devboy/requencer/docs/production-check.md

# Pre-Production PCB Validation Checklist

Run this checklist before ordering PCBs or sourcing parts. Each section specifies what to read, what to check, and what constitutes PASS/WARN/FAIL.

## Output Format

For each section, produce a structured verdict:

```
## Section N: Title
**Verdict: PASS / WARN / FAIL**

| Check | Status | Detail |
|-------|--------|--------|
| ... | PASS/WARN/FAIL | ... |

**Issues found:**
- [Severity] Description — file:line — suggested fix
```

---

## Automated Checks (run first, do not duplicate)

Run these before starting the manual review. Record results for reference.

```bash
make hardware          # Full hardware pipeline (ato build → place → route → 3d → export)
make test-hw           # Unit tests (BOM parser, placement, collision)
cargo test             # Firmware tests (DAC driver, button mapping, MIDI)
```

If any automated check fails, fix before proceeding. Record the output of each for the report.

---

## Section 0: Component & Footprint Audit

**Verdict: PASS** (all CRITICAL, HIGH, and MEDIUM issues resolved)

**Run date:** 2026-03-18 | **Fixes applied:** 2026-03-18

Datasheet-level verification of every component's pin mapping, footprint, 3D model, and circuit usage. Custom footprints and fine-pitch QFN ICs are highest risk.

### CRITICAL — ~~Must fix before fabrication~~ FIXED 2026-03-18

| # | Component | Issue | Status |
|---|---|---|---|
| C1 | **DAC80508ZRTER** | Entire pin mapping wrong (15/16 pins). Remapped to match TI SLASEL1D §6. | **FIXED** |
| C2 | **BAT54S** | Pins 2/3 swapped (CATHODE↔COMMON). Corrected to ANODE=1, CATHODE=2, COMMON=3. | **FIXED** |
| C3 | **2N3904** | LCSC C18536 now KEC (1=E, 2=B, 3=C). Updated pin mapping + manufacturer. | **FIXED** |
| C4 | **PGA2350 I2C** | GP11/GP12 on different I2C instances. Reassigned to GP12(SDA)+GP13(SCL), both I2C0 F3. | **FIXED** |

### HIGH — ~~Should fix before fabrication~~ FIXED 2026-03-18

| # | Component | Issue | Status |
|---|---|---|---|
| H1 | **IS31FL3216A** | I2C address comments swapped for led_b/led_c. Comments corrected to match wiring. | **FIXED** |
| H2 | **PB6149L** | LED polarity confirmed from mechanical drawing: L1(+)=anode=pin5, L2(−)=cathode=pin6. Matches design. Drawing saved to `components/PB6149L/images/`. | **VERIFIED** |
| H3 | **PB6149L** | Switch pin spacing confirmed 5.08mm×5.08mm, pin Ø1.0mm matches footprint drill. Drawing saved to `components/PB6149L/images/`. | **VERIFIED** |

### MEDIUM — ~~Should fix, not blocking~~ FIXED 2026-03-18

| # | Component | Issue | Status |
|---|---|---|---|
| M1 | **PRTR5V0U2X** | SOT-143B pad 1 widened to 1.2mm for polarity ID per SOT-143B spec. | **FIXED** |
| M2 | **DAC80508ZRTER** | Added WQFN-16 3D model reference to footprint. | **FIXED** |
| M3 | **DAC80508ZRTER** | EP pad corrected from 1.7x1.7mm to 1.6x1.6mm per datasheet. | **FIXED** |
| M4 | **R1206** | Added R1206 to SUFFIX_MODEL_MAP in add_3d_models.py. | **FIXED** |
| M5 | **WQP518MA** | Rect pad moved from pin 2 to pin 1 (Tip) per KiCad convention. | **FIXED** |
| M6 | **PJ366ST** | Added missing closing paren to keepout zone polygon in PJ366ST-full.kicad_mod. | **FIXED** |

### LOW — Informational

| # | Component | Issue |
|---|---|---|
| L1 | IS31FL3216A | IN pin left floating. Tie to GND if audio mode unused to prevent noise. |
| L2 | OPA4171AIPWR | 3D model has 0.2625mm X offset — visually verify alignment. |
| L3 | PRTR5V0U2X | LCSC C2827688 manufacturer "TECH PUBLIC" vs design "Nexperia". Functional equivalent. |
| L4 | H11L1S | LCSC C78589 manufacturer "EVERLIGHT" vs .ato "Lite-On". Both valid H11L1S makers. |
| L5 | BAT54S | LCSC C7420333 manufacturer "hongjiacheng" vs .ato "Nexperia". Budget clone. |
| L6 | USB_C_Receptacle | Only 1 shield/mounting pad. Check TYPE-C-31-M-12 datasheet for required mechanical pads. |
| L7 | USB_C_Receptacle | 3D model uses USB4085 as stand-in. Visual alignment unverified. |
| L8 | FPC_18P_05MM | Defined but unused. Dead code (alternate display connector). |
| L9 | ResistorNetwork9 | Defined but unused. Dead code. |
| L10 | FOJAN parts | C2930086 (29.4kΩ) and C2907540 (82Ω 1206) have high LCSC numbers — check stock. |
| L11 | 1206 resistor | Only 1206 part in otherwise all-0402/0603 design. Confirm intentional (power handling). |
| L12 | PGA2350 | LCSC C0000 placeholder — Pimoroni not on LCSC. BOM generation will need manual entry. |
| L13 | Dead generator code | `generate_footprints.py` has unused `make_wqp518ma()` with different pin positions than actual footprint. |

### Components PASSED (no issues)

| Component | Package | Pin mapping | Footprint | Circuit usage |
|---|---|---|---|---|
| IS31FL3216A | QFN-28 (0.45mm) | PASS (all 28+EP) | PASS | PASS |
| OPA4171AIPWR | TSSOP-14 (0.65mm) | PASS (standard quad op-amp) | PASS | PASS |
| 2N7002 | SOT-23 | PASS | PASS | PASS |
| AMS1117-3.3 | SOT-223 | PASS | PASS | PASS |
| B5819W | SOD-123 | PASS | PASS | PASS |
| H11L1S | SOP-6 (2.54mm) | PASS | PASS (wide-body valid for optocoupler) | PASS |
| EurorackPowerHeader16 | 2x8 shrouded | PASS (Doepfer standard) | PASS | PASS |
| ShroudedHeader2x16 | 2x8x2 | PASS (32-pin mirror) | PASS | PASS |
| ShroudedSocket2x16 | 2x8x2 | PASS | PASS | PASS |
| FPC_32P_05MM | 32-pin FPC | PASS (ST7796 match) | PASS | PASS |
| ResArray4x0603 | 0603x4 convex | PASS | PASS | PASS |
| PGA2350 (footprint) | 64-pin PGA | PASS (positions) | PASS | — |
| WQP518MA | THT mono jack | PASS | PASS | PASS |
| PJ366ST | THT stereo jack | PASS | PASS | PASS |
| EC11E | THT encoder | PASS | PASS | PASS |
| PJS008U | MicroSD vertical | PASS (SPI mode) | PASS | PASS |
| Precision resistors | 0603 0.1% | PASS (pitch-critical paths only) | PASS | PASS |

---

## Section 1: RP2350 GPIO Function-Select Compliance

**Why:** The RP2350 has fixed hardware function-select — SPI and UART peripherals can only be assigned to specific GPIOs. This was the #1 class of errors in the 2026-03-10 report (C1-C4).

### Files to read
- `hardware/boards/elec/src/mcu.ato` — all `pga.GPxx ~ signal_name` lines
- `crates/firmware/src/main.rs` — pin assignments (search for `PIN_`)
- `crates/firmware/src/pins.rs` — type aliases for pins
- RP2350 datasheet GPIO function table (Section 1.4.3, Table 2)

### What to check

**SPI0 pins (display + SD card):**

| Function | Valid GPIOs (RP2350) | Check mcu.ato assigns to | Check firmware uses |
|---|---|---|---|
| SPI0_RX (MISO) | GP0, GP4, GP16, GP20 | one of these | same pin |
| SPI0_TX (MOSI) | GP3, GP7, GP19, GP23 | one of these | same pin |
| SPI0_SCK | GP2, GP6, GP18, GP22 | one of these | same pin |
| SPI0_CSn | GP1, GP5, GP17, GP21 | one of these | same pin |

**SPI1 pins (DAC):**

| Function | Valid GPIOs (RP2350) | Check mcu.ato assigns to | Check firmware uses |
|---|---|---|---|
| SPI1_RX (MISO) | GP8, GP12, GP24, GP28 | one of these (if used) | same pin |
| SPI1_TX (MOSI) | GP11, GP15, GP27, GP31 | one of these | same pin |
| SPI1_SCK | GP10, GP14, GP26, GP30 | one of these | same pin |
| SPI1_CSn | GP9, GP13, GP25, GP29 | one of these (if used) | same pin |

**UART1 pins (MIDI):**

| Function | Valid GPIOs (RP2350) | Check mcu.ato assigns to | Check firmware uses |
|---|---|---|---|
| UART1_TX | GP4, GP8, GP12, GP16, GP20, GP24 | one of these | same pin |
| UART1_RX | GP5, GP9, GP13, GP17, GP21, GP25 | one of these | same pin |

**ADC pins (CV inputs):**

| Function | Valid GPIOs (RP2350) | Check mcu.ato assigns to |
|---|---|---|
| ADC4-7 | GP40-GP43 only | cv_a through cv_d |

### Pass criteria
- **PASS:** Every peripheral pin in mcu.ato is on a valid GPIO for that function AND matches firmware
- **WARN:** pins.rs type aliases don't match main.rs (cosmetic but confusing)
- **FAIL:** Any peripheral pin assigned to a GPIO that doesn't support that function, or mcu.ato/firmware mismatch

---

## Section 2: Board-to-Board Connector Pin Matching

**Why:** A single swapped pin on the 2x16 connector means rework or dead board.

### Files to read
- `hardware/boards/elec/src/board-connector.ato` — both `BoardConnectorInterface` and `BoardConnectorSocket`
- `hardware/boards/parts/ShroudedHeader2x16/ShroudedHeader2x16.ato` — header pinout
- `hardware/boards/parts/ShroudedSocket2x16/ShroudedSocket2x16.ato` — socket pinout

### What to check

1. **Pin-for-pin signal matching:** For each pin position (1-32) on both header_a and header_b, verify that the signal name on the Interface (main board male) matches the signal name on the Socket (control board female). Build a comparison table:

   | Pin | Header A Interface (main) | Header A Socket (control) | Match? |
   |-----|--------------------------|--------------------------|--------|
   | 1   | ...                      | ...                      |        |

2. **Physical orientation:** When the main board is below the control board:
   - Male headers point UP from main board
   - Female sockets point DOWN from control board
   - Pin 1 orientation must be consistent (keyed by shroud)
   - Verify the shroud key slot faces the same direction on both boards

3. **Power pin placement:** Verify power pins (GND, 3.3V, 5V, +12V, -12V) are doubled for current capacity and placed at connector edges (not in the middle where signal integrity matters more).

4. **No signal-to-power shorts:** Verify no signal name on one side maps to a power pin on the other side.

### Pass criteria
- **PASS:** All pins match 1:1 between Interface and Socket, orientation is correct
- **FAIL:** Any signal mismatch between corresponding pins, or power pin in wrong position

---

## Section 3: Signal Path Integrity

**Why:** Catches wiring errors, wrong gain, missing protection, floating pins.

### Files to read
- `hardware/boards/elec/src/main.ato` — main board top-level
- `hardware/boards/elec/src/control.ato` — control board top-level
- `hardware/boards/elec/src/mcu.ato` — MCU connections
- `hardware/boards/elec/src/dac-output.ato` — DAC + op-amp + level shifter
- `hardware/boards/elec/src/io-jacks.ato` — jack connections
- `hardware/boards/elec/src/led-driver.ato` — LED driver chain
- `hardware/boards/elec/src/midi.ato` — MIDI I/O circuits
- `hardware/boards/elec/src/input-protection.ato` — CV/clock/reset input protection
- `hardware/boards/elec/src/power.ato` — power supply
- `hardware/boards/elec/src/display.ato` — display connection
- Relevant part .ato files in `hardware/boards/parts/`

### Trace each path end-to-end

For each functional block below, trace the complete signal path from source to destination. Verify correct component values, topology, and power rails at each stage.

#### 3a. Pitch CV (4 channels)
- DAC OUT4-7 → op-amp (gain=2, offset from precision reference) → 470Ω protection → jack tip
- Check: gain resistors (10k/10k for gain=2), offset resistors (15k/10k for -2V offset), 0.1% tolerance on precision path
- Check: op-amp powered from ±12V (not 5V — needs negative swing)
- Check: reference buffer present (no loading on precision divider)
- Expected range: -2V to +8V (10 octaves, 1V/oct)

#### 3b. Gate CV (4 channels)
- DAC OUT0-3 → op-amp (unity gain buffer) → 470Ω protection → jack tip
- Check: unity gain (feedback direct from output to inverting input)
- Expected range: 0-5V

#### 3c. Velocity CV (4 channels)
- DAC OUT → op-amp (gain ≈ 1.6) → protection → jack tip
- Expected range: 0-8V

#### 3d. Mod CV (4 channels)
- DAC OUT → op-amp (inverting gain=2, offset=+5V) → protection → jack tip
- Check: needs negative output, op-amp on ±12V
- Expected range: -5V to +5V

#### 3e. Button scan
- GPIO → 74HC165 chain: CLK (shared), LATCH (shared), DATA (series QH→SER)
- Check: first SR's SER tied to GND, last SR's QH goes to MCU
- Check: CLK_INH tied LOW on all
- Check: pull-ups on all button inputs (via SIP resistor networks)
- Check: unused inputs tied to VCC (no floating)

#### 3f. LED drive
- MCU GPIO → TLC5947 chain: SIN, SCLK, XLAT, BLANK (shared)
- Check: SIN daisy-chains through SOUT→SIN
- Check: BLANK active-high (HIGH = outputs off)
- Check: VCC from 3.3V, LED anodes from 5V
- Check: IREF resistor value → expected max current per channel

#### 3g. MIDI
- **OUT:** MCU UART TX → 220Ω → TRS jack (Tip=data, Ring=VCC per Type A)
- **IN:** TRS jack → 220Ω → optocoupler LED → MCU UART RX
- Check: optocoupler LED polarity (anode toward Ring/VCC source, cathode toward Tip/data)
- Check: protection diode across opto LED (anti-parallel, correct polarity)
- Check: opto output pull-up to 3.3V

#### 3h. Clock/Reset I/O
- **Input:** jack tip → board connector → voltage divider (22k/10k) → BAT54S clamp → 100nF filter → MCU GPIO
- **Output:** MCU GPIO → 1kΩ base resistor → NPN (2N3904) → 1kΩ collector to 5V → jack tip
- Check: divider ratio maps 10V input to < 3.3V
- Check: NPN inverts logic (firmware must account for this)

#### 3i. Display
- MCU SPI0 (MOSI, SCK, CS) + DC + BL + RST → FPC connector
- Check: RST has RC delay circuit (10kΩ × 100nF ≥ 10µs)
- Check: backlight via N-channel MOSFET with gate pull-down

#### 3j. SD card
- MCU SPI0 (MOSI, MISO, SCK) + CS + CD → SD connector
- Check: MISO actually connected (SPI0_RX pin)
- Check: card detect signal routed to MCU

#### 3k. USB-C
- MCU USB DP/DM → 27Ω series → USB-C connector
- Check: 5.1kΩ CC1/CC2 pull-downs present
- Check: ESD protection (PRTR5V0U2X or similar) on data lines
- Check: shield → GND

#### 3l. Encoders
- Encoder A/B/SW → pull-ups (10kΩ to 3.3V) + debounce caps (100nF) → board connector → MCU GPIO
- Check: RC time constant appropriate (10kΩ × 100nF = 1ms)
- Check: active-low push (connects to GND)

#### 3m. CV inputs (4 channels)
- Jack tip → board connector → input protection (22k/10k divider + BAT54S clamp + 100nF) → MCU ADC (GP40-43)
- Check: divider maps ±10V eurorack to 0-3.3V ADC range
- Check: clamp diodes to GND and 3.3V

### Pass criteria
- **PASS:** All signal paths trace correctly end-to-end with correct component values
- **WARN:** Minor issues (e.g., debounce on wrong board, unused MISO floating)
- **FAIL:** Any broken signal path, wrong polarity, missing protection, wrong gain/offset, floating critical pin

---

## Section 4: Power Supply Validation

**Why:** The 2026-03-10 report found the 5V LDO fed from 12V causing thermal overload (C6).

### Files to read
- `hardware/boards/elec/src/power.ato` — regulators, protection diodes
- `hardware/boards/elec/src/main.ato` — power rail connections
- `hardware/boards/elec/src/control.ato` — power distribution on control board
- Regulator datasheets for thermal specs

### What to check

#### 4a. Rail connectivity
For each power rail in the design, verify it reaches every IC that needs it:

| Rail | Source | Check connected to |
|---|---|---|

Fill in from the schematic. For each rail, list every IC power pin that should be connected. Cross-reference the BOM — every IC's supply pin(s) must trace back to the correct rail through the netlist.

#### 4b. Regulator thermal budget

For each regulator, calculate:
- Input voltage × dropout = power dissipation
- Package thermal resistance × dissipation = junction temperature rise
- Junction temp = ambient (40°C for eurorack) + rise

| Regulator | Vin | Vout | Max load (mA) | Dissipation (W) | Package | Max Tj | Verdict |
|---|-----|---|---|---|---|---|---|
| 5V reg | ... | 5V | ... | ... | ... | ... | |
| 3.3V reg  | ... | 3.3V | ... | ... | ... | ... | |

**FAIL if:** Junction temperature > rated max at worst-case load and 40°C ambient.

#### 4c. Bypass capacitors
For every IC in the BOM, verify presence of bypass caps per its datasheet:
- 100nF ceramic close to each power pin (HF decoupling)
- 10µF bulk where needed (MCU, DACs, power entry points)
- Special decoupling where datasheet specifies (e.g., VREF pins, analog supply pins)

Walk the BOM and check each IC — MCU, DACs, LED drivers, shift registers, op-amps, etc. Pay extra attention to:
- ICs with multiple power pins (each needs its own cap)
- Analog supply pins (often need both 100nF + bulk)
- Reference voltage pins (specific cap values/types per datasheet)

#### 4d. Current budget
Sum current per rail and compare to source capacity:

| Rail | Consumers | Total (mA) | Source capacity (mA) | Margin |
|---|---|---|---|---|

Fill in one row per power rail in the design. Sum all consumers from the BOM (use datasheet typical/max current figures). Compare against source capacity (eurorack bus spec or regulator rating).

#### 4e. Cross-board supply isolation
- Check for bulk capacitors (≥10µF) on high-current switching rails (e.g., LED supply) on each board
- Verify high-current switching loads don't share decoupling with precision analog supply

### Pass criteria
- **PASS:** All rails connected, thermal budget OK (Tj < 100°C at 40°C ambient), all ICs decoupled, current budget has >20% margin
- **WARN:** Thermal budget marginal (100-120°C), missing bulk caps on non-critical rails
- **FAIL:** Thermal overload (Tj > max rated), missing bypass on MCU/DAC/ADC, current budget exceeded

---

## Section 5: Component-Purpose Fitness

**Why:** Catches "connected but not usable" errors — components that are wired into the schematic but missing critical connections for their intended function.

### Files to read
- All `.ato` source files under `hardware/boards/elec/src/`
- Part definitions under `hardware/boards/parts/`

### What to check

Walk through every component in the BOM and verify it can actually perform its intended function. Use the categories below as a guide — the specific components will come from the current schematic.

#### Connectors (USB, SD, MIDI, power headers)
- All functional pins connected (not just power)? e.g., USB needs D+/D-, SD needs MISO
- Required pull-ups/pull-downs present? e.g., USB-C CC lines, SD card detect
- ESD protection on external-facing data lines?

#### DACs
- All output channels wired to their intended loads?
- VREF decoupled per datasheet? Internal/external ref configured correctly?
- Control pins (LDAC, CLR, etc.) tied to defined states — not floating?
- Digital IO voltage matches MCU logic level?

#### Op-amps
- All channels in each package used, or unused channels configured as followers (not floating)?
- Supply rails correct for required output swing?

#### Shift registers / daisy-chain ICs
- Chain order correct (data out → data in of next)?
- First chip's serial input tied to defined level?
- Unused parallel inputs tied to VCC or GND?
- Control/inhibit pins in correct state for normal operation?

#### LED drivers
- Current-set resistor present and value matches LED spec?
- Daisy-chain order correct?
- Blank/enable pin has defined boot state (pull-up or pull-down)?

#### Optocouplers
- LED polarity correct (anode/cathode orientation)?
- Output has pull-up resistor?
- Protection diode across LED input?

#### Protection components (clamp diodes, TVS, fuses)
- Connected between signal and both protection rails (GND and VCC)?
- Correct polarity?

#### Transistor switches
- Base/gate resistor present?
- Collector/drain load resistor or connection correct?

#### Power entry
- Reverse-polarity protection on all external supply inputs?

### Pass criteria
- **PASS:** All components connected for intended purpose, no floating pins on active components
- **WARN:** Minor: non-critical feature incomplete (e.g., USB power-only without data during dev)
- **FAIL:** Any component missing critical connections that prevent it from functioning

---

## Section 6: Multi-Button / Simultaneous Input

**Why:** User needs hold-combos (e.g., shift+step) for the UI.

### Files to read
- `hardware/boards/elec/src/led-driver.ato` (shift register chain section)
- `hardware/boards/parts/SN74HC165D/` — part definition
- `crates/firmware/src/main.rs` — button scanning code (search for `buttons`, `shift_register`, `scan`)
- Button wiring in `control.ato`

### What to check

1. **Wiring topology:** Are buttons wired as direct inputs to shift registers (one button per SR input), or in a matrix?
   - Direct wiring: no ghosting possible, any combination works → PASS
   - Matrix wiring: need anti-ghosting diodes on every button → check diodes present

2. **Shift register chain integrity:** 5× 74HC165 = 40 bits. Verify all 40 button positions are accounted for in the firmware bit-to-event mapping.

3. **Scan rate:** Firmware should scan at ≥100 Hz for responsive feel, ≥200 Hz for hold-combo detection. Check the scan interval in firmware.

4. **Pull-ups:** Every button input needs a pull-up (SIP resistor network or discrete). Verify count matches button count.

### Pass criteria
- **PASS:** Direct wiring with pull-ups on all inputs, scan rate ≥200 Hz, all 40 bits mapped
- **WARN:** Scan rate 100-200 Hz (functional but slightly laggy for combos)
- **FAIL:** Matrix wiring without anti-ghosting diodes, floating button inputs, broken SR chain

---

## Section 7: Routing Quality Review

**Why:** DRC passes don't catch analog-digital crosstalk or thermal issues.

### Files to read
- `hardware/boards/elec/layout/control/control.kicad_pcb` — control board layout
- `hardware/boards/elec/layout/main/main.kicad_pcb` — main board layout
- `hardware/boards/board-config.json` — netclass assignments and DRC settings
- `hardware/boards/design-rules.json` — trace width and clearance rules
- Last routing log output (from `make hw-route`)

### What to check

1. **DRC results:** Any violations beyond whitelisted items in board-config.json?
   - Run: `make hw-route` and check DRC output
   - Any unrouted nets = **FAIL**

2. **Analog-digital separation:**
   - Pitch CV traces (DAC → op-amp → jack) should not run parallel to:
     - SPI clock lines (high-frequency switching)
     - LED data lines (TLC5947 SIN/SCLK)
     - Button scan clock
   - Minimum 0.5mm gap between analog and digital traces, or ground guard trace between them

3. **Ground pour connectivity:**
   - No isolated copper islands (disconnected from main ground)
   - Adequate ground pour on both sides of both boards
   - Ground stitching vias present (connects top and bottom ground planes)

4. **Trace widths match netclass:**

   | Netclass | Min width (mm) | Check |
   |----------|---------------|-------|
   | Power | 0.3 | +12V, -12V, +5V, +3.3V, GND |
   | Analog | 0.3 | DAC outputs, op-amp I/O, CV paths |
   | Default | 0.2 | Digital signals |

5. **Thermal relief:** Power pads connected to ground pour with thermal relief (not solid connection) to allow hand soldering of THT components.

### Pass criteria
- **PASS:** Zero DRC violations, no analog-digital parallel runs, connected ground pours, correct trace widths
- **WARN:** Minor: analog trace near digital but with ground between them, cosmetic DRC warnings
- **FAIL:** Unrouted nets, analog traces parallel to SPI clock, isolated ground islands, power traces undersized

---

## Section 8: Firmware-Hardware Pin Compatibility

**Why:** Firmware compiles but won't work if pins don't match the physical PCB.

### Files to read
- `crates/firmware/src/main.rs` — all pin assignments
- `crates/firmware/src/pins.rs` — type aliases
- `crates/firmware/src/dac.rs` — SPI peripheral usage
- `hardware/boards/elec/src/mcu.ato` — physical pin assignments

### What to check

Build a complete comparison table:

| Signal | mcu.ato GPIO | main.rs PIN | Match? | Special requirement | Met? |
|---|---|---|---|---|---|
| SPI0 MOSI | GPx | PIN_x | | SPI0_TX capable | |
| SPI0 MISO | GPx | PIN_x | | SPI0_RX capable | |
| SPI0 SCK | GPx | PIN_x | | SPI0_SCK capable | |
| LCD CS | GPx | PIN_x | | SPI0_CSn capable | |
| LCD DC | GPx | PIN_x | | Any GPIO | |
| LCD BL | GPx | PIN_x | | PWM capable (nice to have) | |
| SPI1 MOSI | GPx | PIN_x | | SPI1_TX capable | |
| SPI1 SCK | GPx | PIN_x | | SPI1_SCK capable | |
| DAC1 CS | GPx | PIN_x | | Any GPIO | |
| DAC2 CS | GPx | PIN_x | | Any GPIO | |
| SD CS | GPx | PIN_x | | Any GPIO | |
| SD Detect | GPx | PIN_x | | Any GPIO | |
| Button CLK | GPx | PIN_x | | Any GPIO | |
| Button LATCH | GPx | PIN_x | | Any GPIO | |
| Button DATA | GPx | PIN_x | | Any GPIO | |
| LED SIN | GPx | PIN_x | | Any GPIO | |
| LED SCLK | GPx | PIN_x | | Any GPIO | |
| LED XLAT | GPx | PIN_x | | Any GPIO | |
| LED BLANK | GPx | PIN_x | | Any GPIO | |
| Enc A (A/B/SW) | GPx | PIN_x | | Any GPIO | |
| Enc B (A/B/SW) | GPx | PIN_x | | Any GPIO | |
| MIDI TX | GPx | PIN_x | | UART1_TX capable | |
| MIDI RX | GPx | PIN_x | | UART1_RX capable | |
| Clock IN | GPx | PIN_x | | ADC or interrupt capable | |
| Clock OUT | GPx | PIN_x | | Any GPIO | |
| Reset IN | GPx | PIN_x | | ADC or interrupt capable | |
| Reset OUT | GPx | PIN_x | | Any GPIO | |
| CV A-D | GP40-43 | PIN_40-43 | | ADC4-7 capable | |

Also check:
- `pins.rs` type aliases match `main.rs` actual usage
- No two signals share the same GPIO
- No GPIO is assigned in firmware but not wired in schematic

### Pass criteria
- **PASS:** All pins match between schematic and firmware, all special requirements met, no conflicts
- **WARN:** pins.rs aliases don't match (cosmetic)
- **FAIL:** Any pin mismatch between schematic and firmware, or special requirement not met

---

## Section 9: Parts Availability & Sourcing Readiness

**Why:** Finding out a part is unavailable after ordering PCBs means wasted boards.

### How to check

```bash
make check-parts BOARD_COUNT=5
```

### What to verify from output

| Check | Criteria | Verdict |
|---|---|---|
| All SMD parts in JLCPCB stock | Quantity available ≥ BOARD_COUNT × qty per board | FAIL if any shows "Out of Stock" |
| JLCPCB library type | Basic/preferred = cheap, extended = $3+ fee per unique part | WARN if >5 extended parts |
| All THT parts have ≥1 supplier | DigiKey, Mouser, TME, or LCSC with stock | FAIL if any THT part has zero suppliers |
| No EOL/NRND parts | Check lifecycle status for all major ICs | FAIL if any active IC is EOL |
| BOM completeness | Every component in schematic appears in BOM | FAIL if any missing |

### Manual spot-checks
For every IC and non-commodity component, manually verify on supplier websites:
- [ ] MCU — availability and lead time
- [ ] DACs — check for NRND/EOL status, verify package matches footprint
- [ ] LED drivers — check package matches footprint
- [ ] Optocouplers — check JLCPCB has exact MPN
- [ ] Display module — verify FPC pinout matches schematic
- [ ] Any connectors with specific mating requirements

### Pass criteria
- **PASS:** All parts in stock, BOM complete, no EOL parts, ≤3 extended JLCPCB parts
- **WARN:** 4-8 extended parts (cost impact), or long lead times (>2 weeks) on any part
- **FAIL:** Any critical part out of stock with no alternative, EOL IC, incomplete BOM

---

## Section 10: Mechanical Fit

**Why:** Board that works electrically but doesn't physically fit in the rack is useless.

### Files to read
- `hardware/faceplate/elec/src/faceplate.ato` — panel dimensions
- `hardware/boards/component-map.json` — component physical dimensions
- `web/src/panel-layout.json` — placed component positions
- `hardware/boards/board-config.json` — board dimensions

### What to check

| Check | Expected | How to verify |
|---|---|---|
| Panel width | 36 HP = 181.88mm ± 0.2mm | Read faceplate.ato board dimensions |
| Panel height | 128.5mm (3U eurorack standard) | Read faceplate.ato board dimensions |
| Mounting holes | 4× at eurorack standard positions (HP 1 and HP 36, 3mm from top/bottom edges) | Check faceplate.ato mounting hole positions |
| Jack holes | 6mm diameter (WQP518MA / PJ366ST barrel fit) | Check faceplate.ato hole sizes |
| Encoder holes | 7mm diameter (EC11E shaft fit) | Check faceplate.ato hole sizes |
| Board stacking clearance | Faceplate → control → main with correct standoff heights | Check 3D assembly (STEP files) |
| THT pin clearance | THT pins from control board don't hit main board components | Visual check in 3D model or calculate from component heights |
| Component height | No component exceeds ~25mm behind panel (rack depth) | Check tallest components (jacks, encoders, electrolytic caps) |
| Rail clearance | No physical components in top/bottom 10mm (rail zone) | Check panel-layout.json positions vs panel edges |

### Pass criteria
- **PASS:** All dimensions match eurorack spec, clearances verified, no collisions in 3D model
- **WARN:** Tight clearances (<1mm) on stacking or THT pins
- **FAIL:** Wrong panel dimensions, component collision, jack/encoder hole size mismatch, components in rail zone

---

## Section 11: Datasheet Compliance Audit

**Why:** Other sections check that signals are connected and components are used for their intended purpose, but don't systematically verify that each IC's datasheet requirements are met. This section catches "wired correctly but violates the datasheet" errors — wrong capacitor type on a reference pin, input voltage above absolute maximum, missing required external components, or boot pin misconfiguration.

### Method

1. List every IC in the BOM (from `.ato` source files and `hardware/boards/parts/`)
2. Download the manufacturer datasheet for each
3. For each IC, work through every check category below
4. Record the specific datasheet section/table that confirms compliance or flags a violation

### 11a. Absolute Maximum Ratings

For every IC, open the "Absolute Maximum Ratings" table in the datasheet and verify:

| Check | How to verify | FAIL if |
|---|---|---|
| Supply voltage | Compare schematic supply rail to rated Vmax | Rail voltage exceeds abs max (even transiently) |
| Input voltage on any pin | Check signal levels at every input pin against rated Vin range | Any input can exceed VCC+0.5V or go below GND-0.5V (unless clamped) |
| Output short-circuit | If outputs can be shorted (user-facing jacks), check for series protection resistors | Unprotected output directly to connector |
| ESD rating | External-facing pins (jacks, USB, MIDI) should have ESD protection | No TVS/ESD diode on connector pins with <2kV HBM rating |
| Junction temperature | Cross-reference with thermal analysis in Section 4b | Operating conditions push Tj above rated max |

### 11b. Power Supply & Decoupling Requirements

For every IC, find the "Recommended Operating Conditions" and "Application Information" sections:

| Check | How to verify | FAIL if |
|---|---|---|
| Supply voltage range | Verify actual rail voltage is within recommended (not just abs max) range | Rail outside recommended operating range |
| Decoupling capacitor values | Compare schematic caps to datasheet "typical application" or "recommended" values | Wrong value, wrong type (e.g., electrolytic where ceramic required), or missing |
| Multiple power pins | Each power pin needs its own decoupling cap, placed close to the pin | Single shared cap for multiple power pins |
| Analog vs digital supply separation | If IC has separate AVDD/DVDD, verify they have independent decoupling paths | Analog and digital supply pins sharing a single cap |
| Reference voltage pins | Check for specific cap type/value requirements (datasheets often specify low-ESR ceramic) | Wrong cap type on VREF (causes noise or instability) |
| Power sequencing | If datasheet specifies power-on sequence (e.g., DVDD before AVDD), verify circuit complies | Incorrect power sequencing possible |

### 11c. Pin Configuration & Control Pins

For every IC, review the pin description table and application circuit:

| Check | How to verify | FAIL if |
|---|---|---|
| Unused pins | Datasheet specifies how to tie unused inputs/outputs | Any pin left floating that should be tied to a defined level |
| Control/config pins | Pins like LDAC, CLR, BLANK, OE, CLK_INH, etc. — verify tied to correct state for intended operation | Control pin floating or in wrong state (IC won't function as expected) |
| Enable/shutdown pins | Check EN, SHDN, PD pins are in the correct state (tied or driven) | Floating enable pin (IC may not start or may randomly shut down) |
| Boot/mode pins | MCU boot mode pins, IC configuration pins — verify match intended boot/config | Wrong mode selected (device boots into wrong state) |
| Reset pins | Check for required pull-up/RC delay per datasheet | Floating or under-specified reset (unreliable startup) |
| Open-drain/collector outputs | Must have external pull-up resistor to appropriate voltage | Missing pull-up (output stuck low or floating) |
| Bidirectional/tristate pins | Verify direction control is correct and default state is safe | Bus contention at startup |

### 11d. Signal Level Compatibility

For every connection between two ICs, verify voltage levels are compatible:

| Check | How to verify | FAIL if |
|---|---|---|
| Logic level thresholds | Compare driver VOH/VOL to receiver VIH/VIL at actual supply voltages | VOH < VIH (logic HIGH not recognized) or VOL > VIL (logic LOW not recognized) |
| Mixed-voltage interfaces | If ICs run on different supply rails (e.g., 3.3V MCU driving 5V logic) | 3.3V output driving HC-family at 5V VCC (VIH = 3.5V, not met by 3.3V driver) |
| Analog signal range | DAC output range vs op-amp input common-mode range; ADC input vs reference voltage | Signal exceeds input common-mode range (clipping, phase inversion) |
| Drive strength vs load | Check source can drive the load (fan-out for digital, impedance for analog) | Source overloaded (voltage droop, signal degradation) |
| Output swing vs required range | Op-amp output swing at actual load vs required signal range | Required output voltage exceeds swing capability at operating supply |

### 11e. Communication Protocol Compliance

For every serial bus (SPI, I2C, UART), verify both ends agree:

| Check | How to verify | FAIL if |
|---|---|---|
| SPI mode (CPOL/CPHA) | Compare MCU firmware SPI config to each slave's datasheet requirement | Mode mismatch (garbled data) |
| SPI clock frequency | Check firmware clock rate against every slave's max SCLK spec | Exceeds any slave's maximum (unreliable at best, damage at worst) |
| Chip select polarity | Active-high vs active-low — verify firmware matches IC requirement | Wrong CS polarity (IC never selected or always selected) |
| I2C address conflicts | If using I2C, verify no two devices share the same address | Address collision (bus errors) |
| UART baud/format | TX/RX baud rate, stop bits, parity match between both ends | Mismatched serial config |
| Daisy-chain order | For chained ICs (shift registers, LED drivers), verify DOUT→DIN wiring order matches firmware bit ordering | Data shifted to wrong device in chain |

### 11f. Timing & Startup Behavior

| Check | How to verify | FAIL if |
|---|---|---|
| Power-on state | What does each IC output at power-on before firmware initializes it? | Unsafe startup state (e.g., DAC outputs full-scale voltage into connected gear, all LEDs on at max current) |
| Reset timing | MCU and peripherals — verify reset pulse width meets datasheet minimum | Reset too short (unreliable initialization) |
| Startup sequencing | If peripherals need to be initialized in a specific order, verify firmware handles this | IC accessed before it's ready (e.g., SPI transfer before power stable) |
| Watchdog/timeout | If IC has internal watchdog or communication timeout, verify firmware services it | Timeout causes unexpected reset or shutdown |

### 11g. Thermal & Layout Requirements

| Check | How to verify | FAIL if |
|---|---|---|
| Thermal pad | If IC has exposed pad, verify PCB footprint connects it correctly (usually to GND with vias) | Thermal pad floating or insufficient vias (overheating) |
| Power dissipation | Calculate worst-case dissipation and check against package thermal rating | Package cannot dissipate heat at max load in enclosed eurorack case |
| Recommended layout | Check datasheet "PCB Layout" section for specific guidance (e.g., keep analog traces short, ground plane under IC) | Critical layout guidance ignored |
| Current-set resistors | For ICs with programmable current (LED drivers, regulators), verify resistor value and tolerance | Wrong current (dim LEDs, wrong voltage, or component damage) |

### Pass criteria
- **PASS:** Every datasheet requirement verified and met for all ICs
- **WARN:** Minor deviations within tolerance (e.g., bypass cap is 220nF instead of 100nF, still functional)
- **FAIL:** Any absolute maximum rating exceeded, missing required external component, wrong pin configuration, or signal level outside rated input range

---

## Section 12: Manufacturing Output Files

**Why:** A correct schematic means nothing if the manufacturing files sent to JLCPCB are wrong. Component rotation errors are the #1 cause of assembly rework, and missing/misformatted files delay orders.

### Files to review
- Gerber output from `make hw-route` (or KiCad export)
- Pick-and-place / CPL files (component position list)
- BOM file formatted for JLCPCB upload
- Drill files (Excellon format)

### What to check

#### 12a. Gerber / Drill Integrity

| Check | How to verify | FAIL if |
|---|---|---|
| Layer count | Open Gerbers in viewer (e.g., gerbv, KiCad Gerber viewer) — count layers | Missing layer (e.g., no silkscreen, no mask) |
| Board outline | F.Cu, B.Cu, Edge.Cuts all present and outline matches expected dimensions | Outline missing or wrong size |
| Drill file | Drill sizes match schematic (via sizes, mounting holes, THT pad holes) | Missing drill file, or wrong hole sizes |
| No stale files | Gerber export date matches latest routing run | Stale Gerbers from a previous revision |

#### 12b. Pick-and-Place / CPL File

| Check | How to verify | FAIL if |
|---|---|---|
| All SMD components present | Count components in CPL vs BOM — should match for SMD parts | Missing components in CPL |
| Rotation offsets | Cross-reference CPL rotations with JLCPCB's known rotation offsets for each package type. Spot-check: QFN (PGA2350), TSSOP (DAC8568), SOT-23 (transistors, diodes), 0402/0603 passives | Any IC likely rotated 90°/180° (pin 1 misaligned) |
| Coordinate origin | Verify CPL origin matches the board origin used by JLCPCB (usually bottom-left of board outline) | Components placed at wrong absolute positions |
| Polarized components | Visually verify orientation of all polarized SMD parts (ICs, diodes, electrolytic caps, LEDs) in CPL preview | Wrong polarity on any component |

#### 12c. BOM Format

| Check | How to verify | FAIL if |
|---|---|---|
| LCSC part numbers | Every SMD component has a valid LCSC/JLCPCB part number | Missing part number (JLCPCB won't place it) |
| Quantities match | BOM quantity × board count matches order | Wrong quantity (short or over-ordered) |
| Designator mapping | BOM designators match CPL designators exactly | Mismatch causes wrong part in wrong location |
| No THT in SMD BOM | THT parts should NOT be in the JLCPCB assembly BOM (hand-soldered) | THT part listed as SMD assembly (will fail or be skipped) |

#### 12d. Fiducial Marks

| Check | How to verify | FAIL if |
|---|---|---|
| Fiducials present | At least 2 (preferably 3) fiducial marks on each board with SMD assembly | No fiducials (machine can't align placement) |
| Fiducial placement | Asymmetric placement (not rotationally symmetric) so machine can determine orientation | Symmetric placement (ambiguous board orientation) |

### Pass criteria
- **PASS:** All files present, rotations verified, BOM/CPL aligned, fiducials correct
- **WARN:** Minor rotation uncertainty on commodity passives (easily caught in JLCPCB review step)
- **FAIL:** Missing CPL/BOM, IC rotation errors, missing fiducials, stale Gerbers

---

## Section 13: Silkscreen & Markings

**Why:** Bad silkscreen wastes debugging time during bring-up and makes hand-assembly error-prone.

### Files to read
- KiCad PCB files for both boards (`control.kicad_pcb`, `main.kicad_pcb`)
- Faceplate layout (`faceplate.kicad_pcb`)

### What to check

| Check | How to verify | FAIL if |
|---|---|---|
| Board version / date | Silkscreen includes version string (e.g., "v0.1 2026-03") on each board | No version marking (can't distinguish revisions) |
| Pin 1 markers | All ICs have pin 1 dot/line on silkscreen near the pad | Missing on any IC (assembly error risk) |
| Connector polarity | Board-to-board headers have clear pin 1 / orientation marking on both boards | No marking (can be plugged in backwards) |
| Power connector polarity | Eurorack power header has -12V/+12V/GND clearly marked | Unmarked power header (reverse polarity risk) |
| Reference designators | Component refs readable, not overlapping pads or other refs, not hidden under components | Unreadable refs (debugging becomes guesswork) |
| Component outlines | Courtyard/silkscreen outlines match actual part footprints | Outlines wrong size (misleading during hand-placement of THT) |

### Pass criteria
- **PASS:** All boards versioned, all connectors marked for polarity, refs readable
- **WARN:** Minor ref overlap on dense areas (functional but annoying)
- **FAIL:** No board version, unmarked board-to-board connectors, unmarked power header

---

## Section 14: EMC & Analog Noise

**Why:** A eurorack module with noisy CV outputs is unusable. Digital switching noise coupling into the 1V/oct pitch path is the most likely source of audible artifacts.

### Files to read
- KiCad PCB layouts (both boards)
- `hardware/boards/elec/src/power.ato` — supply filtering
- `hardware/boards/elec/src/dac-output.ato` — analog output path
- `hardware/boards/design-rules.json` — netclass assignments

### What to check

#### 14a. Ground Plane Strategy

| Check | How to verify | FAIL if |
|---|---|---|
| Continuous ground pour | Both sides of both boards have unbroken ground copper under analog sections | Ground pour missing or severely fragmented under DAC/op-amp area |
| No ground splits under analog ICs | Ground plane continuous under DAC and op-amp footprints (no traces cutting through) | Signal trace bisects ground under DAC or op-amp |
| Ground stitching | Vias connecting top and bottom ground planes, especially around analog sections | No stitching vias near analog path (ground return path too long) |
| Star ground topology | High-current return paths (LEDs, digital switching) don't share ground trace with precision analog | LED driver ground return runs through DAC/op-amp ground area |

#### 14b. Analog-Digital Coupling

| Check | How to verify | FAIL if |
|---|---|---|
| SPI clock isolation | SPI1 clock (DAC) routed away from pitch CV analog traces — minimum 1mm gap or ground guard | SPI clock parallel and adjacent to CV output traces |
| LED driver switching | TLC5947 SCLK/SIN traces not routed near analog output path | LED data lines cross or run parallel to CV path |
| Decoupling placement | 100nF caps physically within 2mm of each IC power pin (not just in schematic) | Decoupling cap on opposite side of board from IC, connected by long trace |
| Analog supply filtering | Separate decoupling on op-amp analog supply pins, not shared with digital rail | Op-amp VCC/VEE decoupling shared with digital IC |

#### 14c. Power Supply Noise

| Check | How to verify | FAIL if |
|---|---|---|
| Regulator output filtering | Bulk + ceramic on each regulator output | Missing ceramic on switching regulator output (HF noise on rail) |
| Cross-board power filtering | Bulk cap on each power rail at board-to-board connector entry point | No filtering at connector (noise couples between boards) |
| Precision reference isolation | DAC VREF decoupling per datasheet, not shared with other analog loads | VREF cap missing or shared |

### Pass criteria
- **PASS:** Continuous ground under analog, decoupling physically close to pins, no digital-analog parallel runs
- **WARN:** Minor: digital trace crosses analog area but at 90° (minimal coupling)
- **FAIL:** Fragmented ground under DAC/op-amps, SPI clock parallel to CV traces, missing decoupling on precision path

---

## Section 15: Board Bring-Up & Test Plan

**Why:** Even a perfectly validated design needs a structured bring-up to catch manufacturing defects before they cause damage. Without a plan, the instinct is to power everything at once — risking a short on one rail taking out an IC on another.

### What to prepare before boards arrive

| Item | Details |
|---|---|
| Lab power supply | Current-limited bench supply, set to 100mA initially |
| Multimeter | Continuity, voltage, resistance checks |
| Oscilloscope | For verifying SPI signals, clock, analog output waveforms |
| Firmware binary | Pre-built and tested on a dev board if possible |
| SWD debugger | For initial flash and debugging (Picoprobe or similar for RP2350) |

### Bring-up sequence

#### Phase 1: Visual inspection (before applying power)
- [ ] Check all SMD components placed and oriented correctly (compare to 3D render)
- [ ] Check solder joints under magnification — bridges, cold joints, tombstoning
- [ ] Check board-to-board connectors for bent pins
- [ ] Continuity check: no short between +12V/GND, -12V/GND, +5V/GND, +3.3V/GND

#### Phase 2: Power supply (main board only, no control board connected)
- [ ] Apply +12V and -12V through eurorack power header, current-limited to 100mA
- [ ] Measure +12V, -12V at test points / regulator inputs
- [ ] Measure +5V regulator output (expected: 5.0V ± 0.1V)
- [ ] Measure +3.3V regulator output (expected: 3.3V ± 0.1V)
- [ ] Check current draw (expected idle: < 50mA total — if significantly higher, stop and investigate)
- [ ] Touch regulators — warm is OK, hot means thermal issue

#### Phase 3: MCU alive
- [ ] Connect SWD debugger to PGA2350
- [ ] Flash minimal blinky firmware (toggle a known GPIO)
- [ ] Verify GPIO toggles with scope/LED
- [ ] Flash full firmware, verify USB enumeration (if USB connected)

#### Phase 4: Board-to-board connection
- [ ] Power off, connect control board via board-to-board headers
- [ ] Power on, re-check all voltage rails (current limit still on)
- [ ] Check current draw with both boards (expected: < 150mA — adjust based on LED count)

#### Phase 5: Peripheral verification
- [ ] **SPI display:** Send test pattern, verify display shows pixels
- [ ] **Button scan:** Press each button, verify firmware reads correct bit position
- [ ] **LEDs:** Light each LED individually, verify correct position and color
- [ ] **Encoders:** Turn each encoder, verify firmware reads direction correctly
- [ ] **DAC outputs:** Set known DAC values, measure with multimeter at jack outputs
  - Gate: 0V and 5V
  - Pitch: -2V and +8V (verify full range)
  - Velocity: 0V and 8V
  - Mod: -5V and +5V
- [ ] **MIDI:** Send MIDI note from computer, verify firmware receives it
- [ ] **Clock I/O:** Send 5V square wave into clock input, verify firmware detects edges; trigger clock output, verify 5V square wave at jack
- [ ] **CV inputs:** Apply known voltages (0V, 1.65V, 3.3V), verify ADC reads correct values
- [ ] **SD card:** Insert card, verify firmware can read/write a test file

### Test points
Verify these test points exist on the PCB (if not, add them before manufacturing):

| Signal | Board | Purpose |
|---|---|---|
| +5V | Main | Verify regulator |
| +3.3V | Main | Verify regulator |
| +12V | Main | Verify power input |
| -12V | Main | Verify power input |
| GND | Both | Probe reference |
| SPI1 SCK (DAC) | Main | Verify DAC communication |
| DAC OUT (1 channel) | Main | Verify analog output |
| SWD CLK/DIO | Main | Firmware debug access |

### Pass criteria
- **PASS:** All phases complete, all peripherals functional, voltages within spec
- **WARN:** Minor: one LED position swapped (firmware fix), or one button reads inverted
- **FAIL:** Power rail out of spec, MCU won't flash, any peripheral completely non-functional

---

## Section 16: Sandwich Stack Assembly

**Why:** Three PCBs stacking (faceplate + control + main) with board-to-board connectors creates mechanical constraints that don't show up in per-board validation.

### Files to read
- 3D assembly STEP files (`hardware/boards/build/3d/`)
- Board-to-board connector datasheets (ShroudedHeader2x16 / ShroudedSocket2x16)
- `hardware/boards/board-config.json` — board dimensions
- `hardware/faceplate/elec/src/faceplate.ato` — faceplate dimensions

### What to check

#### 16a. Connector Keying & Orientation

| Check | How to verify | FAIL if |
|---|---|---|
| Shroud key alignment | Both header (main) and socket (control) shroud keys face the same direction when boards are stacked | Key orientation prevents mating, or allows 180° insertion |
| Pin 1 alignment | Pin 1 on header aligns with pin 1 on socket when stacked (not mirrored) | Pin 1 on opposite corners (all signals swapped) |
| Silkscreen marking | Both boards have clear pin 1 / key direction marking visible after assembly | No visible marking (can only verify by disassembly) |

#### 16b. Mechanical Clearances

| Check | How to verify | FAIL if |
|---|---|---|
| Mated height | Board-to-board connector mated height (from datasheet) matches standoff height | Standoffs too short (boards under stress) or too tall (connectors don't fully mate) |
| THT pin clearance | THT component pins protruding below control board don't hit components on main board top side | Pin contacts component (short circuit or mechanical damage) |
| Component height — control bottom | No SMD component on control board bottom exceeds available gap above main board top | Component collision between boards |
| Component height — main top | Tallest component on main board top fits within gap below control board bottom | Component collision |

#### 16c. Assembly Order

Document the correct assembly sequence:
1. Solder SMD on both boards (JLCPCB)
2. Solder THT components on control board (jacks, buttons, encoders, headers)
3. Mount standoffs to main board
4. Mate control board onto main board via board-to-board connectors
5. Attach faceplate with spacers/nuts through jack and encoder mounting hardware
6. Connect eurorack power cable

Verify:
- [ ] THT components can be soldered after SMD assembly (no access blocked)
- [ ] Board-to-board connectors accessible for mating after THT is soldered
- [ ] Faceplate attachment doesn't require disassembling the stack

### Pass criteria
- **PASS:** Connectors keyed correctly, clearances verified in 3D model, assembly sequence feasible
- **WARN:** Tight clearance (<0.5mm) between boards — functional but fragile
- **FAIL:** Connector keying allows wrong insertion, component collision between boards, assembly impossible without rework

---

## Section 17: Component Documentation & Traceability

**Why:** Missing or stale datasheets, README files, and footprint mismatches create confusion during bring-up and make future revisions error-prone. Every component should have a clear paper trail from datasheet → .ato pin mapping → footprint → 3D model.

### Files to walk

For every component directory under `hardware/boards/elec/src/components/` (skip `_archive/`):

### 17a. Datasheet & Reference Material

| Check | How to verify | FAIL if |
|---|---|---|
| Datasheet present | Each component dir has a PDF or a link in README to manufacturer datasheet | No datasheet reference for any active component |
| Datasheet matches LCSC part | The datasheet covers the exact MPN in the .ato `has_part_picked` trait | Datasheet is for a different variant (e.g., different package, different voltage rating) |
| Pin mapping matches datasheet | Walk every `signal X ~ pin N` in the .ato against the datasheet pin table | Any pin assignment contradicts the datasheet |

### 17b. Footprint & Symbol Alignment

| Check | How to verify | FAIL if |
|---|---|---|
| Footprint file exists | `.kicad_mod` referenced in `is_atomic_part` trait exists in the component directory | Missing footprint file |
| Symbol file exists | `.kicad_sym` referenced in `is_atomic_part` trait exists in the component directory | Missing symbol file |
| Pad count matches .ato | Number of `signal ~ pin N` declarations (plus commented-out NC pins) equals the footprint pad count | Mismatch suggests missing or extra pins |
| 3D model present | `.step` file exists for THT and QFN/BGA components (SMD passives may use KiCad defaults) | Missing 3D model for a component that protrudes through faceplate or affects stacking clearance |
| Footprint dimensions match datasheet | Spot-check pad pitch, pad size, and courtyard against the datasheet recommended land pattern | Pad pitch or size significantly off from datasheet |

### 17c. README Accuracy

For each component and circuit directory that has a README:

| Check | How to verify | FAIL if |
|---|---|---|
| README exists | Each component dir with custom footprint/symbol has a README explaining the part | Missing README for a non-trivial custom component |
| Part description current | README describes the actual part used (not a previously-considered alternative) | README describes a different part than what's in the .ato |
| Pin mapping documented | README pin table (if present) matches the .ato file | Contradictory pin information |
| Circuit READMEs current | Each circuit dir README describes the current topology, component values, and design rationale | README describes an old topology (e.g., different LED driver, different optocoupler) |
| No stale references | No mentions of replaced components (e.g., "6N138" when H11L1S is used, "TLC5947" when IS31FL3216A is used, "DAC8568" when DAC80508 is used) | Stale component references that could mislead during debugging |

### 17d. Cross-Reference Consistency

| Check | How to verify | FAIL if |
|---|---|---|
| component-map.json complete | Every component address referenced in board .ato files has an entry in `component-map.json` with correct group/label/dimensions | Missing entries cause export_layout.py to skip components |
| LCSC part numbers valid | Spot-check 5-10 LCSC part numbers from .ato files against lcsc.com — verify they resolve to the correct part | LCSC number points to wrong part or is discontinued |
| No orphan components | Components in `components/` (non-archive) are all instantiated somewhere in `circuits/` or `boards/` | Unused component clutters BOM and may confuse procurement |

### Pass criteria
- **PASS:** Every active component has datasheet reference, matching footprint/symbol, accurate README, and valid LCSC part number
- **WARN:** Minor README staleness (e.g., outdated comment, old alternative mentioned in passing) that doesn't affect correctness
- **FAIL:** Missing datasheet for any IC, pin mapping contradicts datasheet, footprint missing or wrong dimensions, README describes a different circuit topology than what's built

---

## Final Report Template

```markdown
# Production Validation Report — Requencer
**Date:** YYYY-MM-DD
**Verdict:** PASS / DO NOT MANUFACTURE

## Summary
| Section | Verdict | Critical Issues |
|---------|---------|-----------------|
| 1. GPIO Function-Select | | |
| 2. Connector Pin Matching | | |
| 3. Signal Path Integrity | | |
| 4. Power Supply | | |
| 5. Component Fitness | | |
| 6. Multi-Button Input | | |
| 7. Routing Quality | | |
| 8. Firmware-Pin Compat | | |
| 9. Parts Availability | | |
| 10. Mechanical Fit | | |
| 11. Datasheet Compliance | | |
| 12. Manufacturing Output Files | | |
| 13. Silkscreen & Markings | | |
| 14. EMC & Analog Noise | | |
| 15. Board Bring-Up & Test | | |
| 16. Sandwich Stack Assembly | | |
| 17. Component Documentation | | |

## Automated Check Results
(paste output of make hw-build, hw-place, hw-route, check-parts, test-hw, cargo test)

## Detailed Findings
(one sub-section per check section, using the format specified above)

## Action Items
### Must Fix (FAIL items)
1. ...

### Should Fix (WARN items)
1. ...

## Comparison with Previous Reports
- 2026-03-10 report: 6 critical issues (C1-C6) — status of each fix
```
