devboy/requencer/docs/superpowers/plans/2026-03-23-bypass-cap-placement-priority.md

# Bypass Capacitor Placement Priority — Implementation Plan

> **For agentic workers:** REQUIRED SUB-SKILL: Use superpowers:subagent-driven-development (recommended) or superpowers:executing-plans to implement this plan task-by-task. Steps use checkbox (`- [ ]`) syntax for tracking.

**Goal:** Place bypass/decoupling capacitors immediately after their associated IC and target them at the IC's power pins, not the centroid of all power net members.

**Architecture:** Three coordinated changes — (1) net-based detection of bypass caps and their IC association in `connectivity.py`, (2) ordering interleave helper in `wavefront.py`, (3) power-net neighbor filtering in `_best_position_and_rotation`. Threading via new `power_nets` field on `Board` → `PlacementContext.bypass_map()`.

**Tech Stack:** Python, placer library (`hardware/boards/scripts/placer/`)

**Spec:** `docs/superpowers/specs/2026-03-23-bypass-cap-placement-priority-design.md`

---

### File Structure

| File | Action | Responsibility |
|---|---|---|
| `placer/dtypes.py` | Modify | Add `power_nets: frozenset[str]` field to `Board` |
| `placer/connectivity.py` | Modify | Add `identify_bypass_caps()` function |
| `placer/strategies/wavefront.py` | Modify | Add `_interleave_bypass_caps()` helper; modify `_best_position_and_rotation` and all 3 strategies |
| `placer/context.py` | Modify | Add `bypass_map()` method using lazy cache |
| `placer/kicad_bridge.py` | Modify | Accept and pass `power_nets` in `build_placer_board` |
| `placement/place_components.py` | Modify | Pass `power_nets` through to `build_placer_board` |
| `placer/tests/test_connectivity.py` | Modify | Add tests for `identify_bypass_caps` |
| `placer/tests/test_wavefront.py` | Create | Tests for `_interleave_bypass_caps` and bypass targeting |

---

### Task 1: Add `power_nets` field to `Board` dataclass

**Files:**
- Modify: `hardware/boards/scripts/placer/dtypes.py:112-123`

- [ ] **Step 1: Add field to Board**

In `placer/dtypes.py`, add `power_nets` field to the `Board` dataclass after `smd_side`:

```python
@dataclass
class Board:
    """The complete placement problem definition."""
    width: float   # mm
    height: float  # mm
    components: list[Component] = field(default_factory=list)
    nets: list[Net] = field(default_factory=list)
    rotation_nets: list[Net] = field(default_factory=list)  # includes power nets
    zones: list[BlockedZone] = field(default_factory=list)
    affinity_rules: list[AffinityRule] = field(default_factory=list)
    clearance: float = 0.5      # mm, minimum gap between components
    tht_clearance: float = 0.0  # mm, extra clearance around THT parts
    smd_side: str = "both"      # "front", "back", or "both"
    power_nets: frozenset[str] = field(default_factory=frozenset)  # power/bus net names
```

- [ ] **Step 2: Verify existing tests still pass**

Run: `cd /Users/devboy/dev/devboy/requencer/hardware/boards/scripts && PYTHONPATH=. python -m pytest placer/tests/ -v`

Expected: All existing tests pass (new field has default `frozenset()` — backwards compatible).

---

### Task 2: Thread `power_nets` through bridge and orchestrator

**Files:**
- Modify: `hardware/boards/scripts/placer/kicad_bridge.py:204-229`
- Modify: `hardware/boards/scripts/placement/place_components.py:480-488`

- [ ] **Step 1: Add `power_nets` param to `build_placer_board`**

In `placer/kicad_bridge.py`, add `power_nets` parameter to `build_placer_board` and pass it to `Board`:

```python
def build_placer_board(
    board_w: float,
    board_h: float,
    bridges: dict[str, ComponentBridge],
    nets: list[Net],
    affinity_rules: list[AffinityRule] | None = None,
    zones: list[BlockedZone] | None = None,
    clearance: float = 0.5,
    tht_clearance: float = 0.0,
    smd_side: str = "both",
    rotation_nets: list[Net] | None = None,
    power_nets: frozenset[str] | None = None,
) -> Board:
    """Build a placer Board from extracted data."""
    components = [b.component for b in bridges.values()]
    return Board(
        width=board_w,
        height=board_h,
        components=components,
        nets=nets,
        rotation_nets=rotation_nets or [],
        zones=zones or [],
        affinity_rules=affinity_rules or [],
        clearance=clearance,
        tht_clearance=tht_clearance,
        smd_side=smd_side,
        power_nets=power_nets or frozenset(),
    )
```

- [ ] **Step 2: Pass `power_nets` from orchestrator**

In `placement/place_components.py`, around line 480-488 where `build_placer_board` is called, add the `power_nets` argument:

```python
    placer_board = build_placer_board(
        board_w, board_h, bridges, nets,
        affinity_rules=affinity_rules,
        zones=zones,
        clearance=0.5,
        tht_clearance=tht_extra,
        smd_side=placer_smd_side,
        rotation_nets=rotation_nets,
        power_nets=frozenset(power_nets),
    )
```

- [ ] **Step 3: Verify existing tests still pass**

Run: `cd /Users/devboy/dev/devboy/requencer/hardware/boards/scripts && PYTHONPATH=. python -m pytest placer/tests/ -v`

Expected: All pass — `power_nets` has a default.

---
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
