devboy/requencer/docs/superpowers/plans/2026-03-15-placement-strategy-refactor.md

# Placement Strategy Interface Refactor — Implementation Plan

> **For agentic workers:** REQUIRED: Use superpowers:subagent-driven-development (if subagents available) or superpowers:executing-plans to implement this plan. Steps use checkbox (`- [ ]`) syntax for tracking.

**Goal:** Centralize cross-cutting placement concerns (collision tracking, offset math, legalization, anti-affinity) into a `BoardState` toolkit class, make the orchestrator board-agnostic, and move all hardcoded fixed positions into `board-config.json`.

**Architecture:** Strategies receive `place(components: list[ComponentInfo], board: BoardState, params: dict) -> dict[str, Placement]`. `BoardState` wraps the collision tracker and provides toolkit methods (check_collision, find_legal_position, connectivity_target, anti_affinity_cost, register_placement, legalize). The orchestrator loads config, builds enriched ComponentInfo, constructs BoardState, calls the strategy, and writes back.

**Tech Stack:** Python 3.11+, KiCad pcbnew API, pytest

**Spec:** `docs/superpowers/specs/2026-03-15-placement-strategy-refactor-design.md`

**Note on commits:** CLAUDE.md says "Do NOT make git commits." Commit steps below are guidance for the user — the implementing agent should NOT commit unless the user explicitly asks. Let the user decide when to commit or roll back.

---

## File Map
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
