devboy/requencer/docs/superpowers/plans/2026-03-11-faceplate-connectors.md

# Faceplate Connectors Implementation Plan

> **For agentic workers:** REQUIRED: Use superpowers:subagent-driven-development (if subagents available) or superpowers:executing-plans to implement this plan. Steps use checkbox (`- [ ]`) syntax for tracking.

**Goal:** Move display, USB-C, and SD card from main board to control board with faceplate-accessible connectors, routing all signals through the existing board-to-board connector spare pins.

**Architecture:** Three new component parts (FPC ZIF connector, vertical USB-C, vertical MicroSD) get added to the control board. The main board loses its on-board display header, USB-C receptacle, and SD card slot — those signals now cross through Header A spare pins (9-16, 17, 20, 21) to the control board. The faceplate gets updated cutout dimensions.

**Tech Stack:** Atopile 0.14 (.ato schematics), KiCad (footprints/symbols), TypeScript (web preview rendering)
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
