devboy/requencer/docs/research/images/st7796-40pin-photo.webp

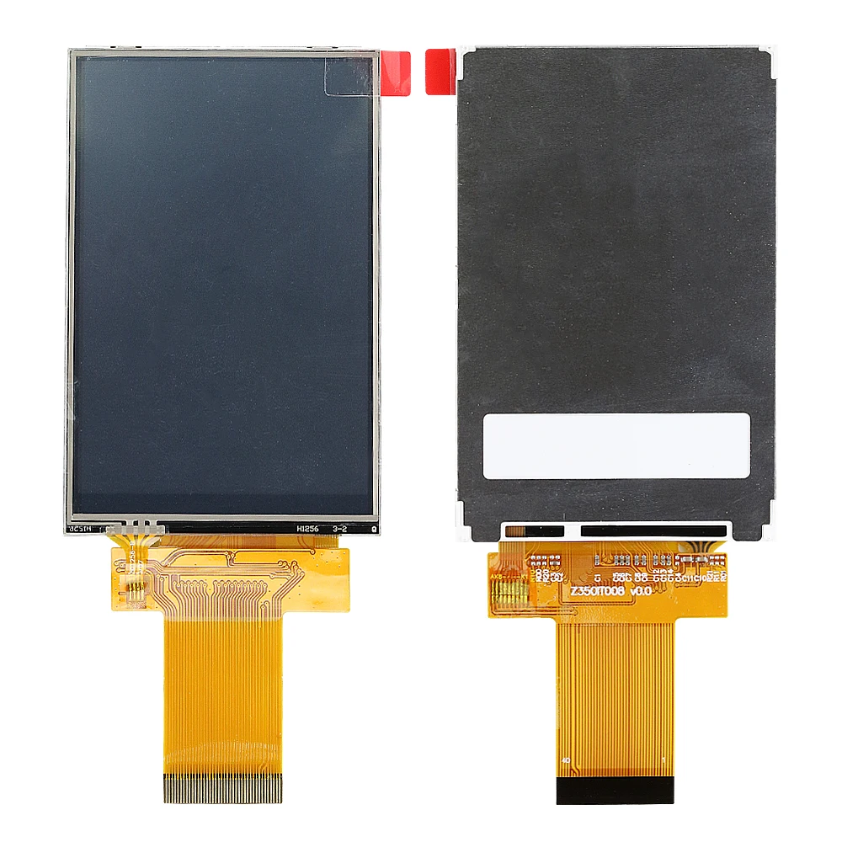
docs/research/images/st7796-40pin-photo.webp
