devboy/requencer/hardware/boards/elec/src/components/2N7002/README.md

# 2N7002 — 60V 300mA N-Channel MOSFET

## Overview
Logic-level N-channel MOSFET in SOT-23 package. Vgs threshold 1-2.5V allows direct 3.3V drive. Used for LCD backlight switching.

## Key Specifications
| Parameter | Value |
|---|---|
| Package | SOT-23 |
| Vds | 60V |
| Id | 300mA |
| Vgs(th) | 1-2.5V |
| LCSC | C8545 |

## Datasheet
- [LCSC page](https://www.lcsc.com/product-detail/C8545.html)

## Used In
- [`control.ato`](../boards/control/control.ato) — LCD backlight switching
