devboy/requencer/hardware/boards/elec/src/components/BAT54S/README.md

# BAT54S — Dual Series Schottky Diode

## Overview
Dual series Schottky diode in SOT-23 package. Used for input protection clamping on CV/gate inputs.

## Key Specifications
| Parameter | Value |
|---|---|
| Package | SOT-23 |
| LCSC | C7420333 |

## Datasheet
- [LCSC page](https://www.lcsc.com/product-detail/C7420333.html)

## Used In
- [`input-protection.ato`](../circuits/input-protection/input-protection.ato) — input voltage clamping
