devboy/requencer/hardware/boards/elec/src/components/PB6149L/README.md

# PB6149L — 6x6mm Illuminated Tactile Switch with LED

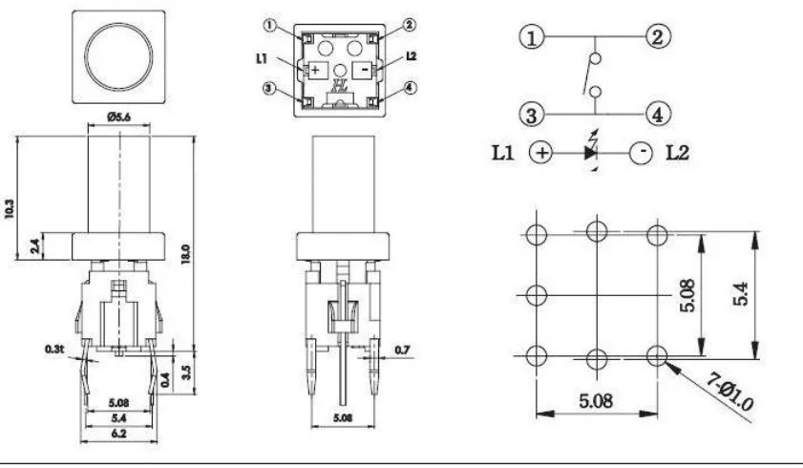
[picture p11: hardware/boards/elec/src/components/PB6149L/images/pb6149l-white-led.jpg]
PB6149L white LED with transparent cap


## Overview
Through-hole SPST momentary pushbutton with an integrated single-color LED (common anode). Translucent round cap, 5.6mm diameter, 10.3mm tall. Dual bridged switch contacts (pins 1+2 and 3+4 internally connected).

## Why This Part
Generic illuminated tact switch in 6x6mm form factor fits the dense eurorack panel layout. Combines button + LED in one component, reducing part count and simplifying placement. Not available from JLCPCB assembly — hand-soldered THT.

## Key Specifications
| Parameter | Value |
|---|---|
| Package | 6x6mm THT, 10.3mm tall |
| Switch | SPST momentary, dual-bridged contacts |
| LED | Single-color, common anode |
| Cap | Translucent round, 5.6mm dia |
| Source | AliExpress (GJW store) |

## Sourcing
- **AliExpress:** GJW store (search "PB6149L illuminated tact switch")
- **JLCPCB/LCSC:** Not available (THT hand-solder part)

## Used In
- [`button-scan.ato`](../circuits/button-scan/button-scan.ato) — 32 instances for step buttons, track buttons, and function buttons
