devboy/requencer/hardware/boards/elec/src/components/PJ366ST/README.md

# PJ366ST — 3.5mm TRS Stereo Jack

## Overview
QingPu WQP-PJ366ST 3.5mm stereo (TRS) jack, vertical through-hole mount. Same Thonkiconn form factor as the mono WQP518MA but with tip, ring, and sleeve contacts. Unswitched.

## Why This Part
TRS jack required for MIDI TRS Type A standard (tip=data, ring=+V, sleeve=shield). Same physical footprint as the mono jacks used elsewhere on the panel, maintaining visual consistency.

## Key Specifications
| Parameter | Value |
|---|---|
| Package | THT vertical mount |
| Type | 3.5mm stereo (TRS), unswitched |
| Contacts  | Tip, Ring, Sleeve |
| LCSC | C2907129 |

## Sourcing
- **JLCPCB/LCSC:** C2907129
- **AliExpress:** Available (search "WQP-PJ366ST" or "thonkiconn stereo")

## Used In
- [`midi.ato`](../circuits/midi/midi.ato) — 2 instances for MIDI TRS input and output jacks
