devboy/requencer/hardware/boards/elec/src/components/ShroudedHeader2x16/README.md

# ShroudedHeader2x16 — 2x16 Shrouded Pin Header

## Overview
32-pin (2x16) shrouded through-hole pin header, 2.54mm pitch. Keyed to prevent reverse insertion. Male side of the board-to-board connector between control and main boards.

## Key Specifications
| Parameter | Value |
|---|---|
| Pitch | 2.54mm |
| Pins | 32 (2x16) |
| Type | Through-hole, shrouded, keyed |
| LCSC | C2939229 |

## Datasheet
- [LCSC page](https://www.lcsc.com/product-detail/C2939229.html)

## Used In
- [`board-connector.ato`](../circuits/board-connector/board-connector.ato) — main board side of board-to-board connection
