devboy/requencer/hardware/boards/elec/src/components/ShroudedSocket2x16/README.md

# ShroudedSocket2x16 — 2x16 Shrouded Pin Socket

## Overview
32-pin (2x16) shrouded through-hole pin socket (female IDC), 2.54mm pitch. Keyed to prevent reverse insertion. Mates with ShroudedHeader2x16 on the main board.

## Key Specifications
| Parameter | Value |
|---|---|
| Pitch | 2.54mm |
| Pins | 32 (2x16) |
| Type | Through-hole, shrouded, keyed, female |
| LCSC | C2685037 |

## Datasheet
- [LCSC page](https://www.lcsc.com/product-detail/C2685037.html)

## Used In
- [`board-connector.ato`](../circuits/board-connector/board-connector.ato) — control board side of board-to-board connection
