devboy/requencer/hardware/boards/elec/src/components/WQP518MA/README.md

# WQP518MA — 3.5mm Mono Jack (Thonkiconn)

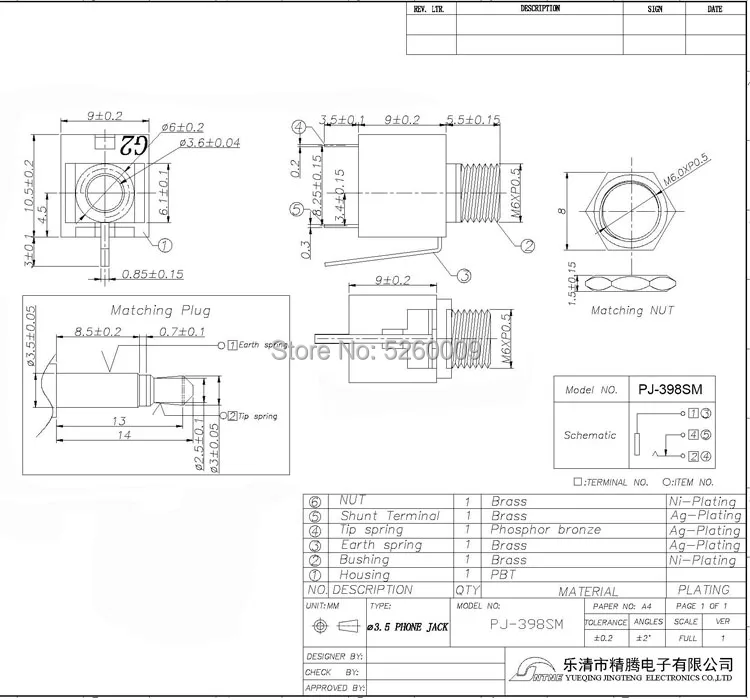
[picture p12: hardware/boards/elec/src/components/WQP518MA/images/wqp518ma-jacks.jpg]
WQP518MA mono jacks


## Overview
Standard eurorack 3.5mm mono jack (Thonkiconn style) by QingPu. Through-hole vertical mount with tip, sleeve, and normally-closed switch contact that opens when a plug is inserted.

## Why This Part
The de facto standard eurorack jack. Same footprint as the original PJ398SM Thonkiconn but widely available and cheaper. Compatible with all standard eurorack patch cables.

## Key Specifications
| Parameter | Value |
|---|---|
| Package | THT vertical mount |
| Type | 3.5mm mono (TS) with switch |
| Contacts  | Tip, Sleeve, Switch (NC) |
| LCSC | C5378060 |

## Sourcing
- **JLCPCB/LCSC:** C5378060
- **AliExpress:** Widely available (search "WQP518MA thonkiconn")

## Used In
- [`io-jacks.ato`](../circuits/io-jacks/io-jacks.ato) — 24 instances for gate, pitch, velocity, mod, clock, reset, and CV jacks
