devboy/requencer/hardware/boards/elec/src/components/_archive/PTS645SM43SMTR92/README.md

# PTS645SM43SMTR92 — Tactile Switch (Archived)

## Overview
C&K PTS645 series SMD tactile switch, 6x6mm body, 4.3mm height. Was used as BOOTSEL button.

## Key Specifications
| Parameter | Value |
|---|---|
| Package | SMD 6x6mm, 4.3mm height |
| LCSC | C221880 (JLCPCB extended) |
| MPN | PTS645SM43SMTR92 (C&K) |

## Archived Files
- `SW_SPST_PTS645.kicad_mod` — KiCad footprint (6x6mm, pad span 6.7mm)
