devboy/requencer/hardware/boards/elec/src/components/_archive/FPC_18P_05MM/README.md

# FPC_18P_05MM — 18-Pin 0.5mm FPC ZIF Connector

## Overview
Bottom-contact FPC ZIF connector, 18-pin, 0.5mm pitch. Designed to mate with the JC3248A035N-1 display FPC ribbon cable.

## Key Specifications
| Parameter | Value |
|---|---|
| Pitch | 0.5mm |
| Pins | 18 |
| Contact | Bottom |
| LCSC | C262657 |

## Datasheet
- [LCSC page](https://www.lcsc.com/product-detail/C262657.html)

## Used In
Not currently imported in any circuit .ato file. Part defined for the smaller round display option.
