devboy/requencer/hardware/boards/scripts/build/rotation_check/back_0.png

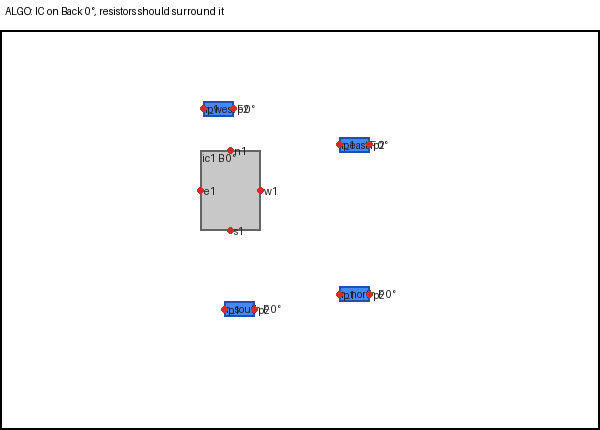
hardware/boards/scripts/build/rotation_check/back_0.png
