devboy/requencer/hardware/boards/scripts/tests/test_collision_tracker.py

"""Tests for CollisionTracker."""

from placement.helpers import CollisionTracker


class TestRegisterAndCollide:
    def test_no_collision_when_separated(self):
        t = CollisionTracker(100, 100, clearance=0.5)
        t.register(10, 10, 5, 5, "F", False, "a")
        assert not t.collides(30, 30, 5, 5, "F")

    def test_collision_same_side(self):
        t = CollisionTracker(100, 100, clearance=0.5)
        t.register(10, 10, 5, 5, "F", False, "a")
        assert t.collides(13, 10, 5, 5, "F")

    def test_no_collision_opposite_sides_smd(self):
        t = CollisionTracker(100, 100, clearance=0.5)
        t.register(10, 10, 5, 5, "F", False, "a")
        assert not t.collides(10, 10, 5, 5, "B")

    def test_tht_collides_both_sides(self):
        t = CollisionTracker(100, 100, clearance=0.5)
        t.register(10, 10, 5, 5, "F", True, "tht")  # THT = both
        assert t.collides(12, 10, 5, 5, "F")
        assert t.collides(12, 10, 5, 5, "B")

    def test_smd_vs_tht_collision(self):
        t = CollisionTracker(100, 100, clearance=0.5)
        t.register(10, 10, 5, 5, "B", False, "smd")
        # THT checking against existing SMD — "both" conflicts with "B"
        assert t.collides(12, 10, 5, 5, "F", is_tht=True)

    def test_clearance_respected(self):
        t = CollisionTracker(100, 100, clearance=2.0)
        t.register(10, 10, 4, 4, "F", False, "a")
        # Registered rect: (10-2-2, ...) to (10+2+2, ...) = (6, 8) to (14, 12)
        # Query at 17: body from 15 to 19 — no overlap with (6..14)
        assert not t.collides(17, 10, 4, 4, "F")
        # Query at 15: body from 13 to 17 — overlaps with (6..14)
        assert t.collides(15, 10, 4, 4, "F")
        # Query at 14.5: body from 12.5 to 16.5 — overlaps
        assert t.collides(14.5, 10, 4, 4, "F")

    def test_extra_padding(self):
        t = CollisionTracker(100, 100, clearance=0.5, extra_padding=2.0)
        t.register(10, 10, 4, 4, "F", False, "a")
        # Total clearance = 2.5mm. Registered rect: (5.5..14.5)
        # Query at 15: body 13..17 — overlaps with 5.5..14.5
        assert t.collides(15, 10, 4, 4, "F")
        # Query at 17: body 15..19 — no overlap
        assert not t.collides(17, 10, 4, 4, "F")
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
